cecilsmith/GPS-MINPOINT/2_Code/src/utils.h

/*
 * Course Number: EE2361
 * Term: Spring 2024
 * Lab/assignment number: Final Project
 * Short Program Description: Contains functions that are commonly used utilities.
 */

#ifndef UTILS_H
#define UTILS_H

#ifdef __cplusplus
extern "C"
{
#endif

    // Delays for the specified number of milliseconds
    void delay_ms(unsigned int ms);

#ifdef __cplusplus
}
#endif

#endif // UTILS_H
